AlinS1/TSC-OpenBook/Images/OpenBook_with_screen.png

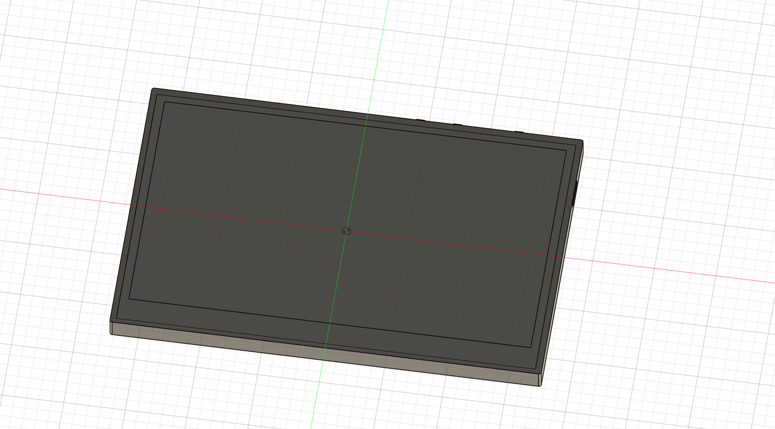
Images/OpenBook_with_screen.png
