AlinS1/TSC-OpenBook/Images/OpenBook_components.png

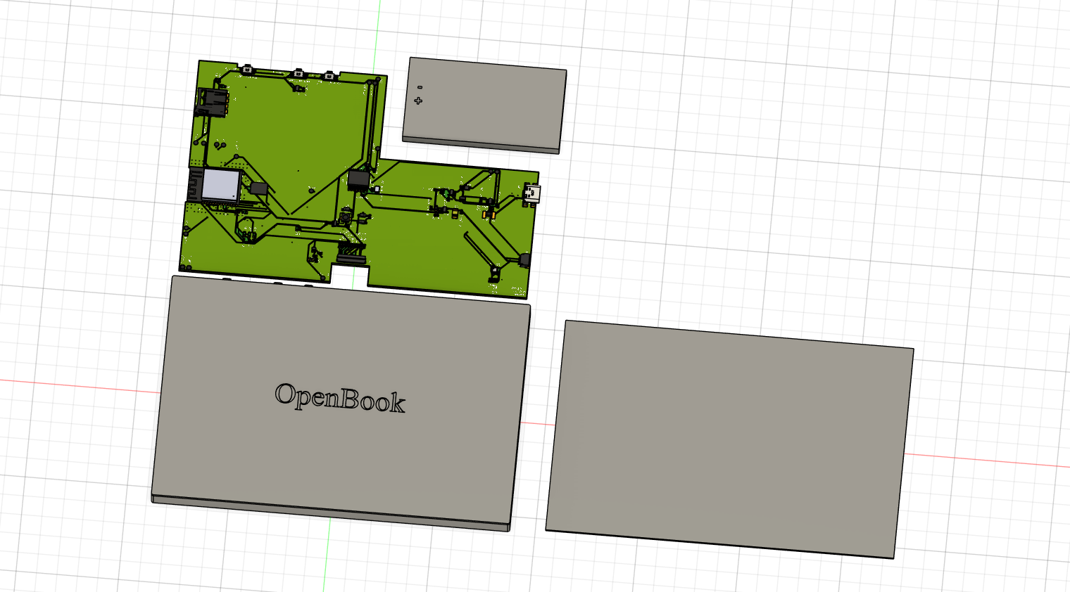
Images/OpenBook_components.png
